vasudevtechnologies/NayanSathi-AI-Smart-Glasses/Circuit_Diagram/Circuit_diagram.png

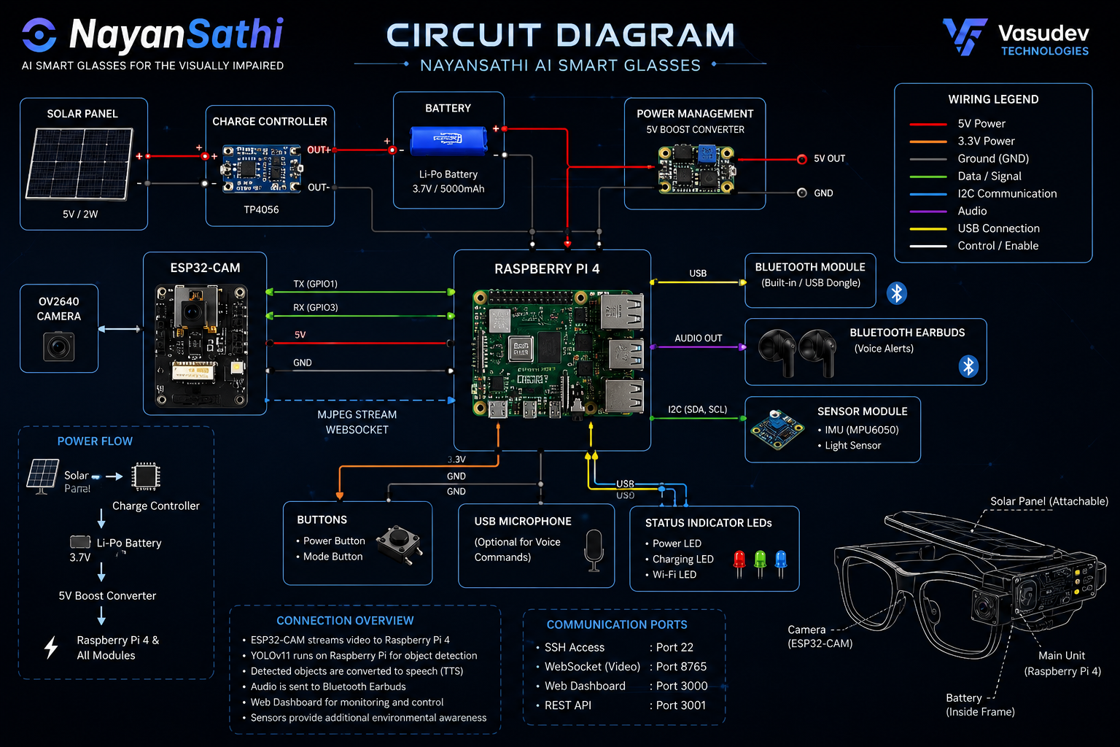
Circuit_Diagram/Circuit_diagram.png
