vasudevtechnologies/NayanSathi-AI-Smart-Glasses/Images/product.png

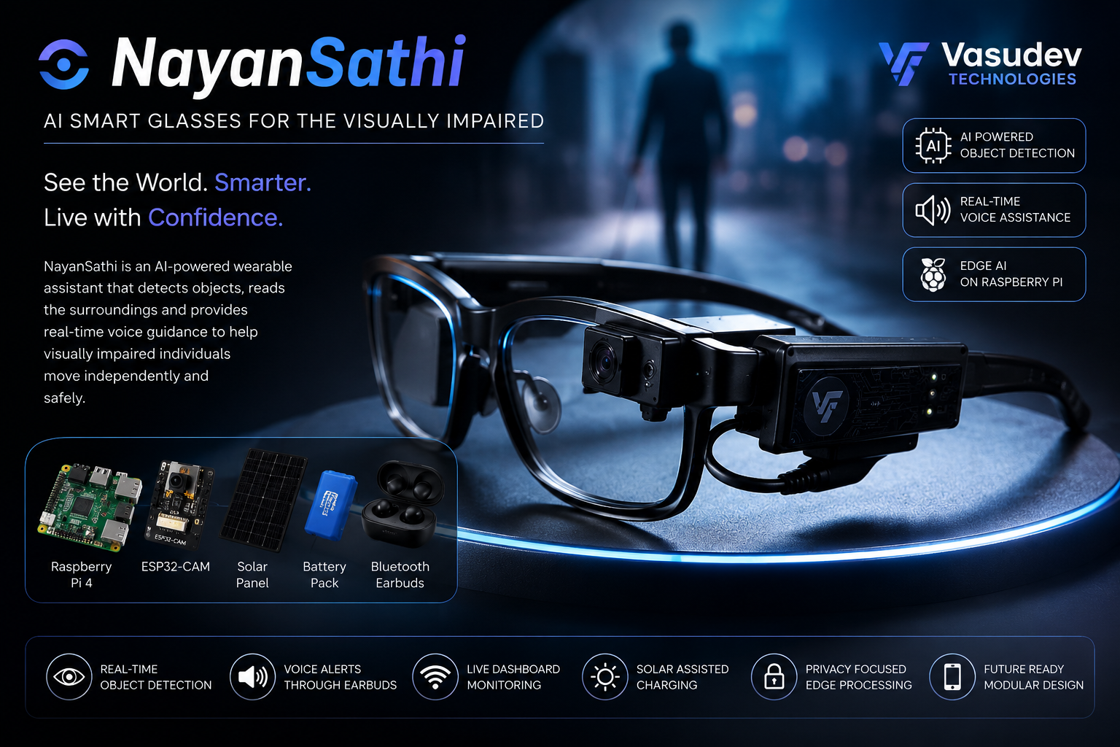
Images/product.png
