vasudevtechnologies/NayanSathi-AI-Smart-Glasses/Images/smart-glasses-top-view.png

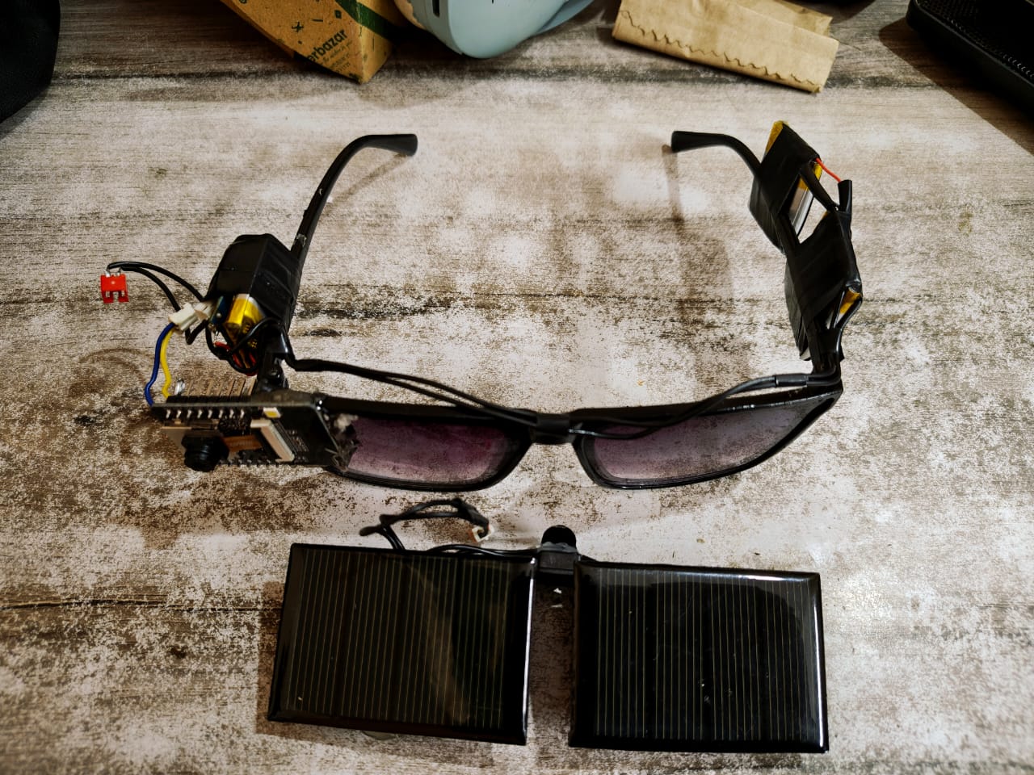
Images/smart-glasses-top-view.png
