vasudevtechnologies/NayanSathi-AI-Smart-Glasses/Images/yolo-detection-banana-demo.png

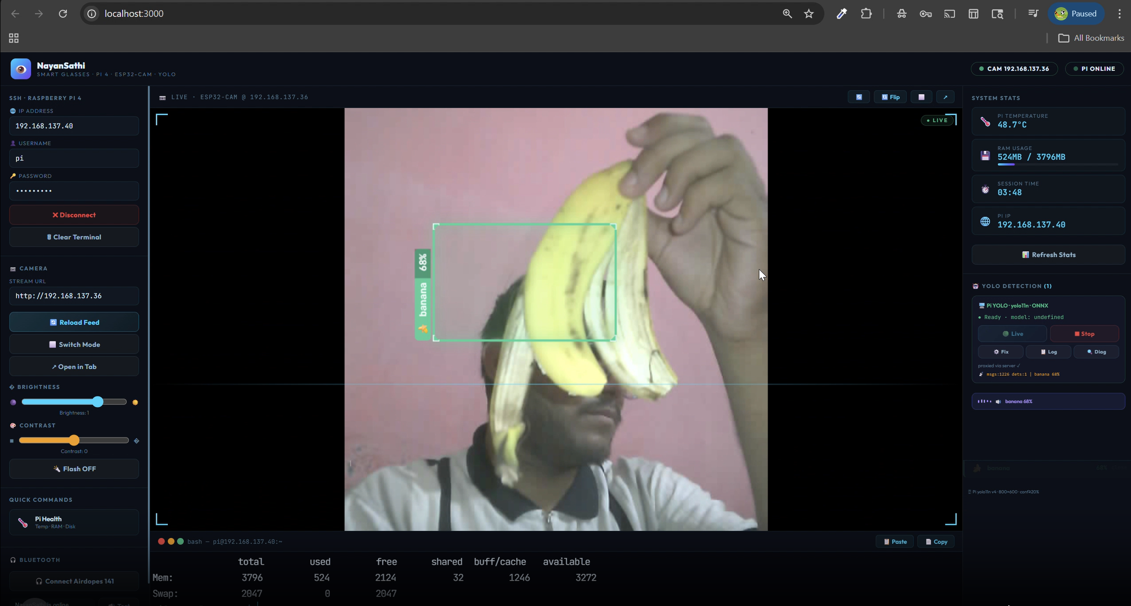
Images/yolo-detection-banana-demo.png
