vasudevtechnologies/NayanSathi-AI-Smart-Glasses/Images/yolo-detection-person-demo.png

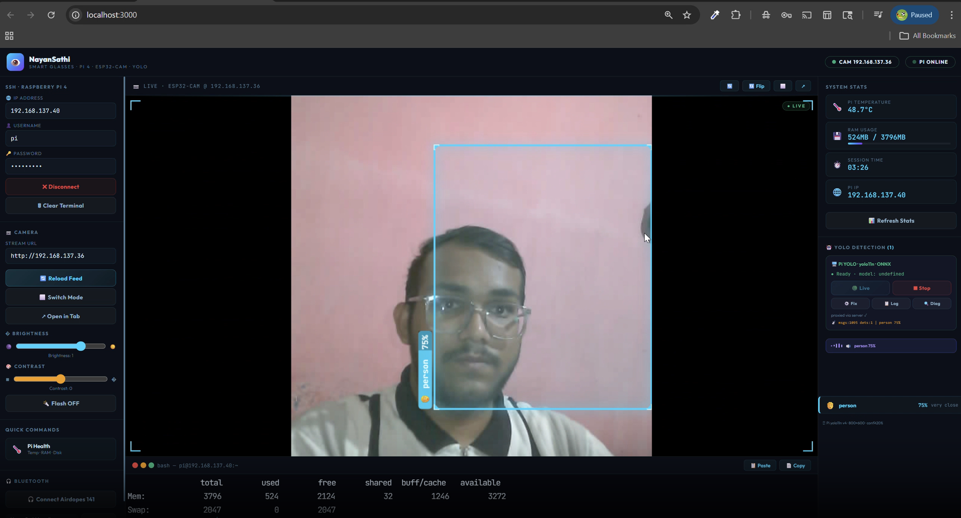
Images/yolo-detection-person-demo.png
