vasudevtechnologies/NayanSathi-AI-Smart-Glasses/website/images/day-night.png

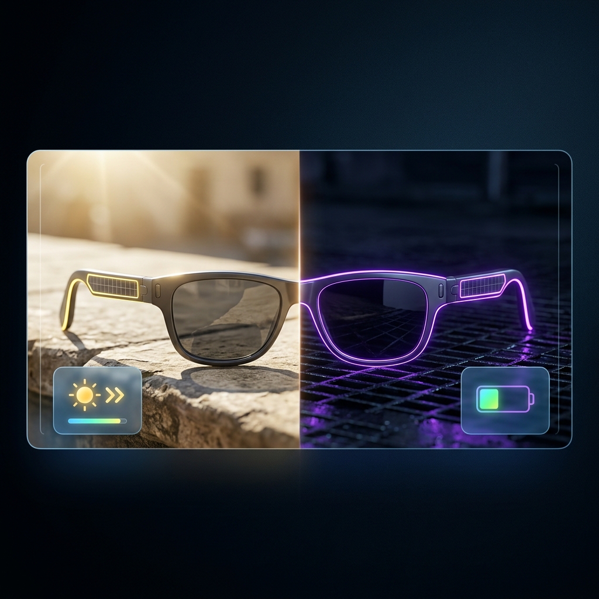
website/images/day-night.png
