vasudevtechnologies/NayanSathi-AI-Smart-Glasses/website/images/hero.png

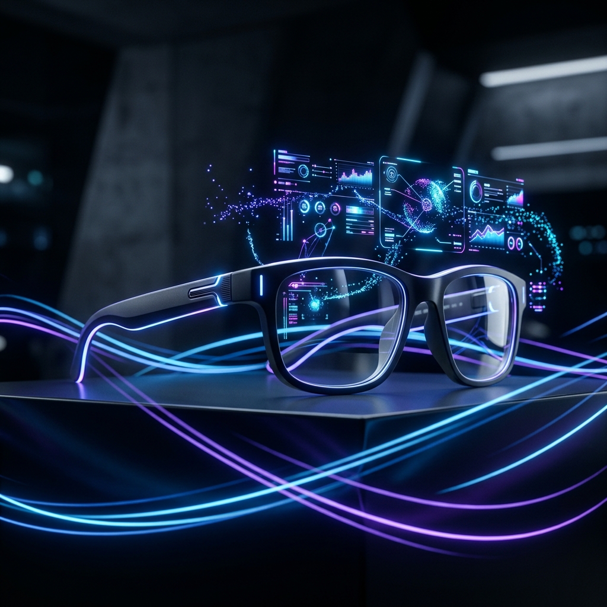
website/images/hero.png
