vasudevtechnologies/NayanSathi-AI-Smart-Glasses/website/images/product-showcase.png

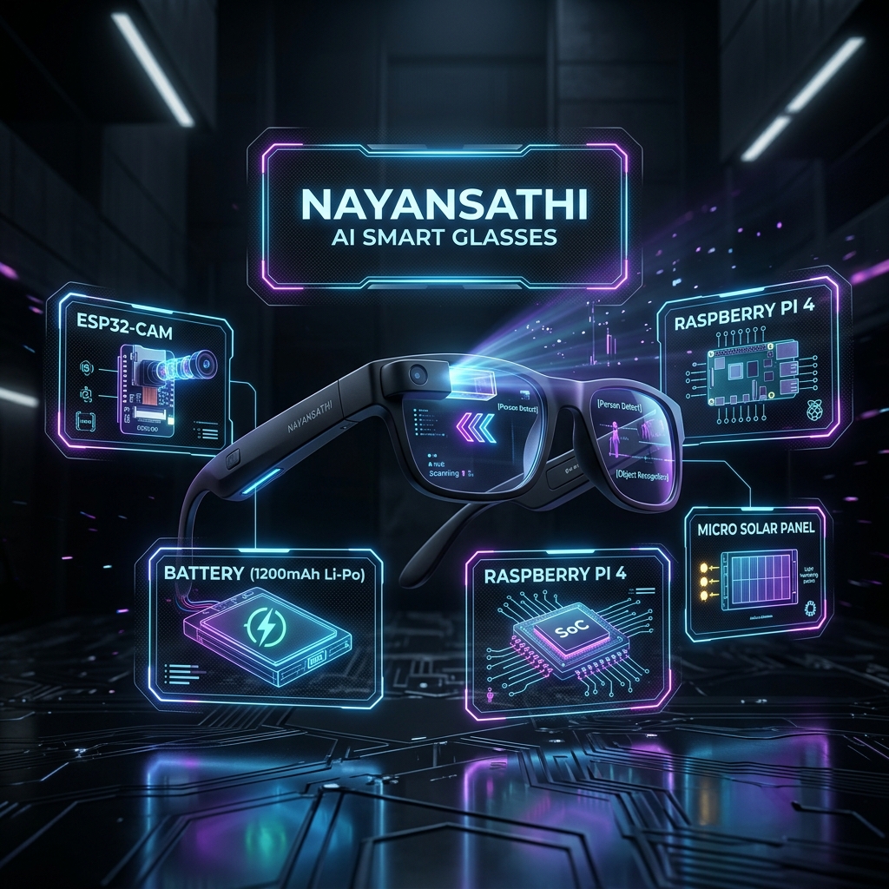
website/images/product-showcase.png
